dodo-12-37/TrackSense_AppEmbarque/Photos du projet/Application embarquée.png

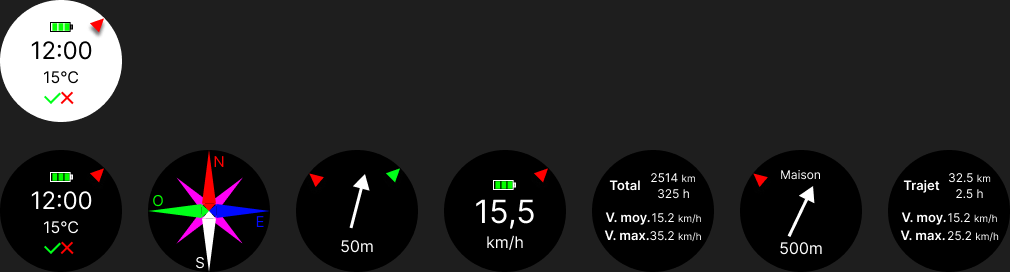
Photos du projet/Application embarquée.png
