dodo-12-37/TrackSense_AppEmbarque/Références Composants/GC9A01 - TFT LCD Display Module/Composant Acheté - Écran GC9A01.png

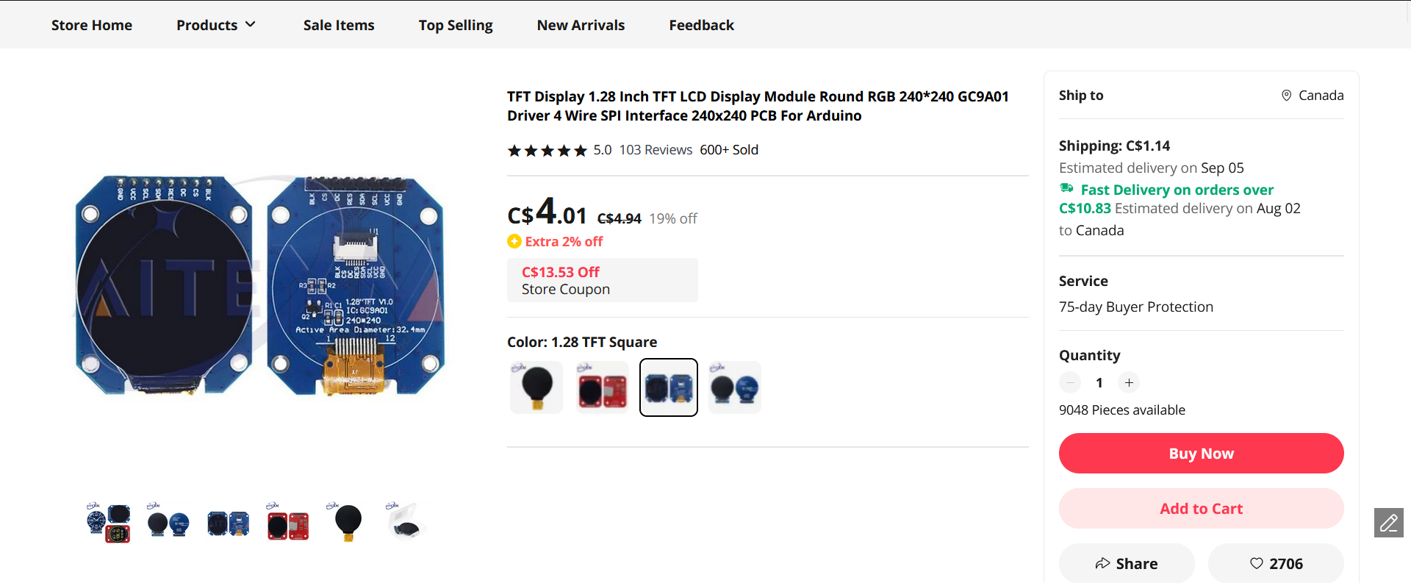
Références Composants/GC9A01 - TFT LCD Display Module/Composant Acheté - Écran GC9A01.png
