dodo-12-37/TrackSense_AppEmbarque/Références Composants/GC9A01 - TFT LCD Display Module/Connection Similar GC9A01 Modules.png

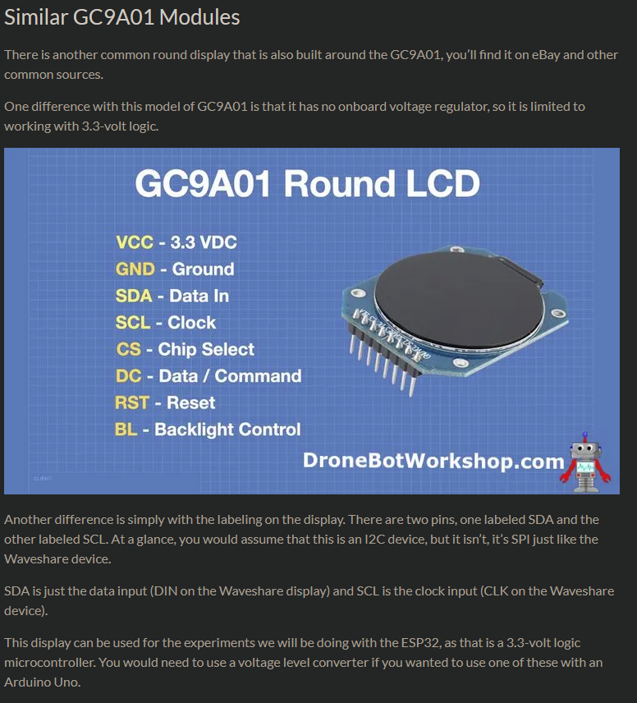
Références Composants/GC9A01 - TFT LCD Display Module/Connection Similar GC9A01 Modules.png
