dodo-12-37/TrackSense_AppEmbarque/Références Composants/GC9A01 - TFT LCD Display Module/Diagramme PINs.png

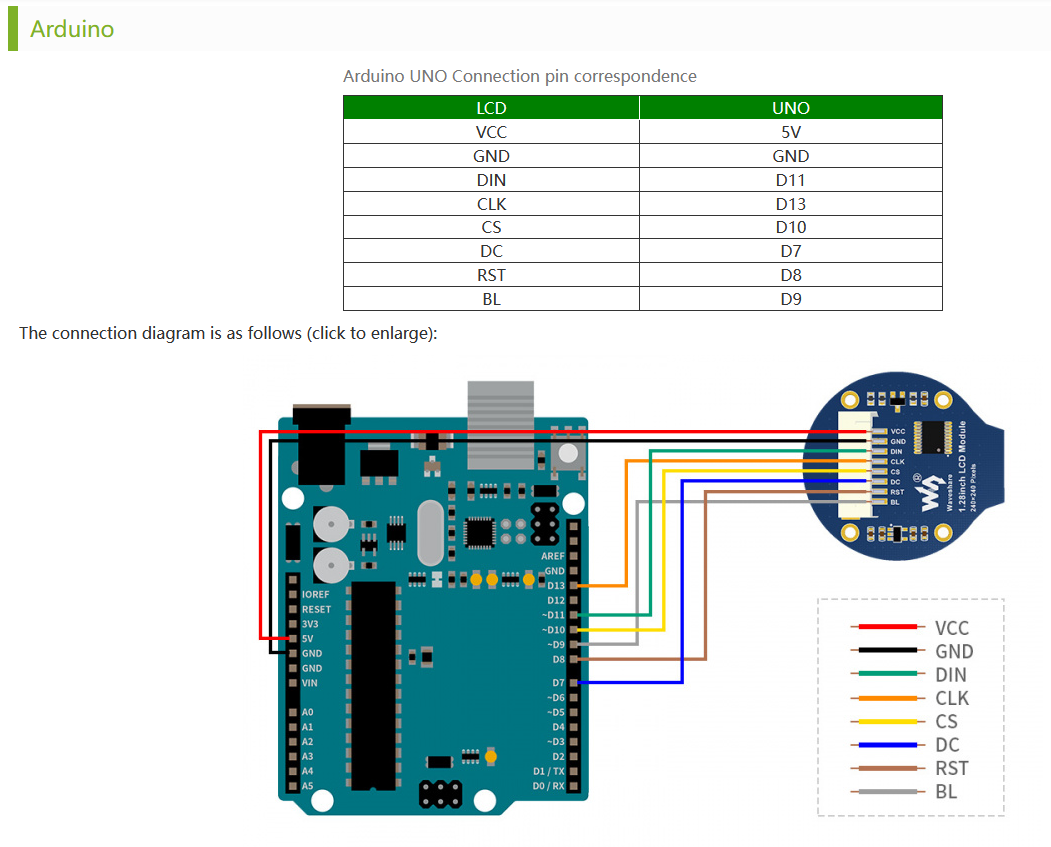
Références Composants/GC9A01 - TFT LCD Display Module/Diagramme PINs.png
