dodo-12-37/TrackSense_AppEmbarque/Références Composants/GC9A01 - TFT LCD Display Module/Dimension Sensor ER-TFTM1.28-1 with No Touch Panel Outline Drawing.png

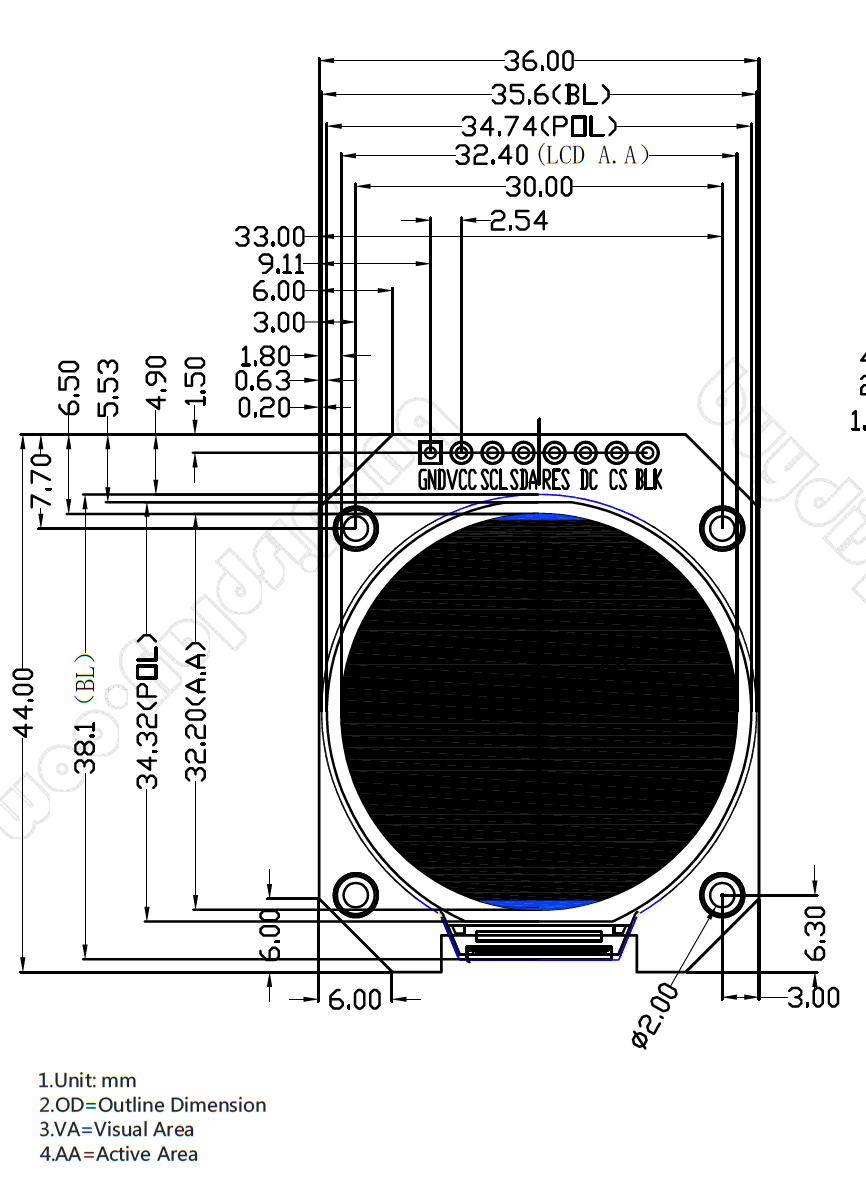
Références Composants/GC9A01 - TFT LCD Display Module/Dimension Sensor ER-TFTM1.28-1 with No Touch Panel Outline Drawing.png
