dodo-12-37/TrackSense_AppEmbarque/Références Composants/GC9A01 - TFT LCD Display Module/IPS-LCD-1.28-240x240-Round-Display-GC9A01-Square-PCB.jpg

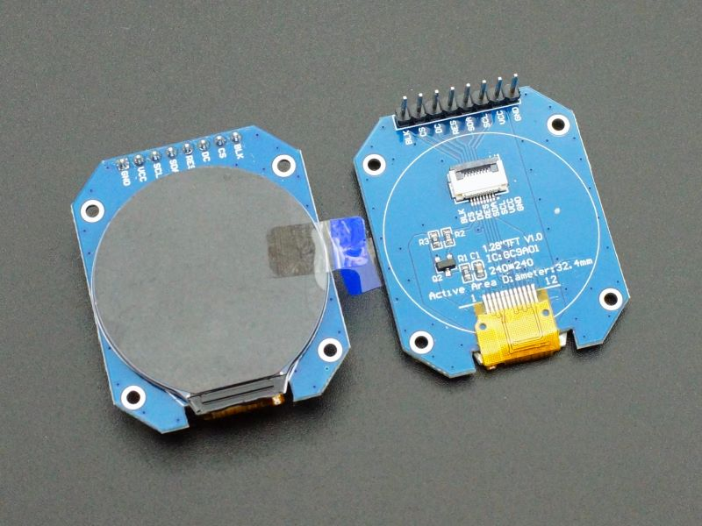
Références Composants/GC9A01 - TFT LCD Display Module/IPS-LCD-1.28-240x240-Round-Display-GC9A01-Square-PCB.jpg
