dodo-12-37/TrackSense_AppEmbarque/Références Composants/GC9A01 - TFT LCD Display Module/TFT LCD Display Module GC9A01 - Mesure Physique.jpg

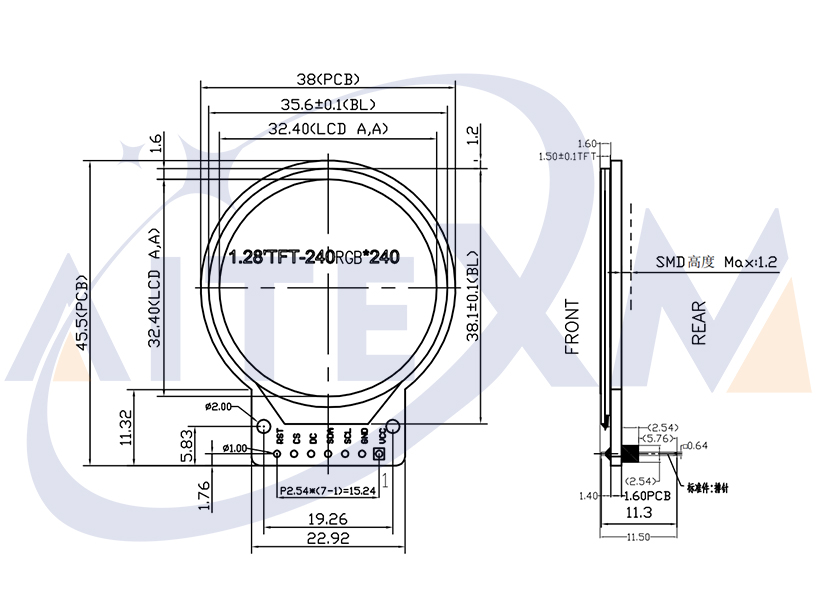
Références Composants/GC9A01 - TFT LCD Display Module/TFT LCD Display Module GC9A01 - Mesure Physique.jpg
