dodo-12-37/TrackSense_AppEmbarque/Références Composants/GY-87 - Accéléromètre, Gyroscope, Boussole & Température/Composant Acheté - GY-87.png

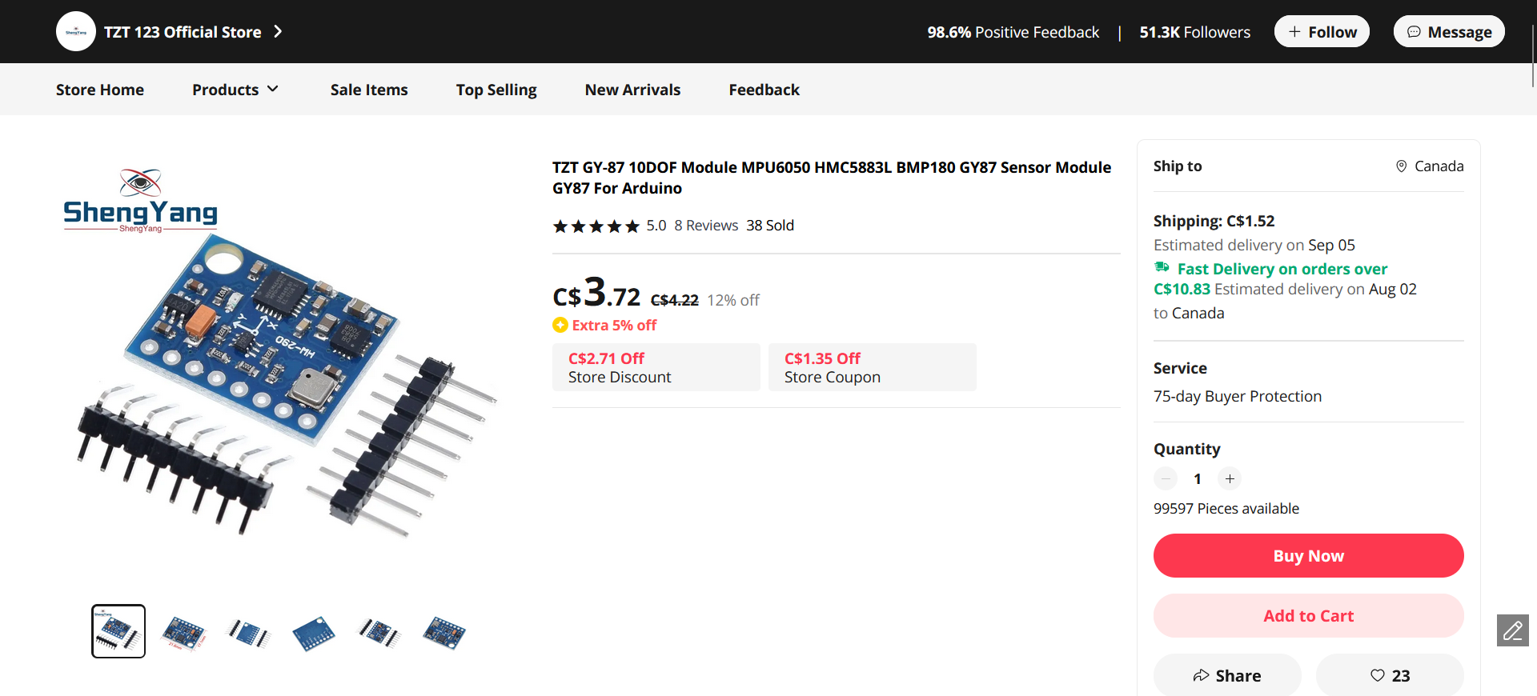
Références Composants/GY-87 - Accéléromètre, Gyroscope, Boussole & Température/Composant Acheté - GY-87.png
