dodo-12-37/TrackSense_AppEmbarque/Références Composants/GY-87 - Accéléromètre, Gyroscope, Boussole & Température/Dessous Sensor.jpg

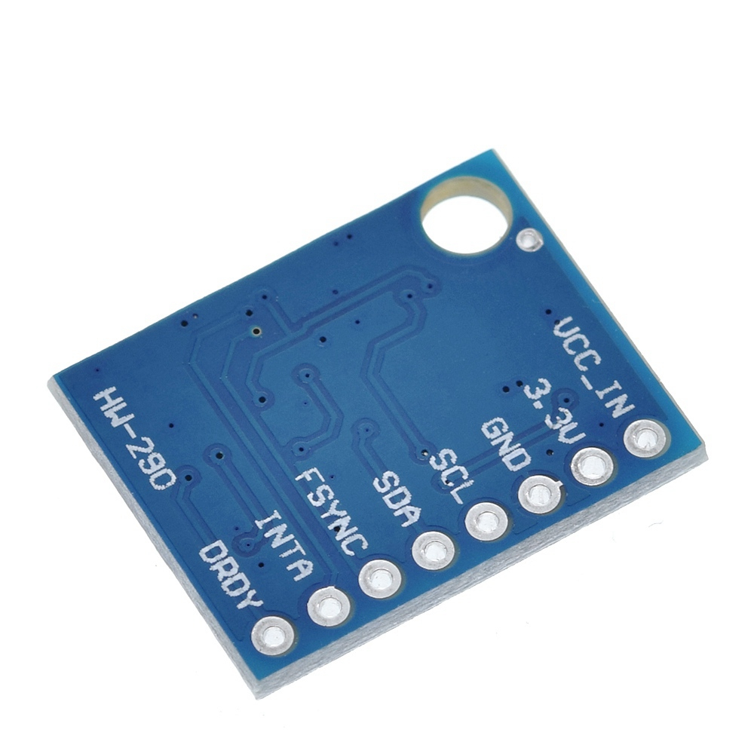
Références Composants/GY-87 - Accéléromètre, Gyroscope, Boussole & Température/Dessous Sensor.jpg
