dodo-12-37/TrackSense_AppEmbarque/Références Composants/GY-87 - Accéléromètre, Gyroscope, Boussole & Température/GY-87-Module-wire-4.jpg

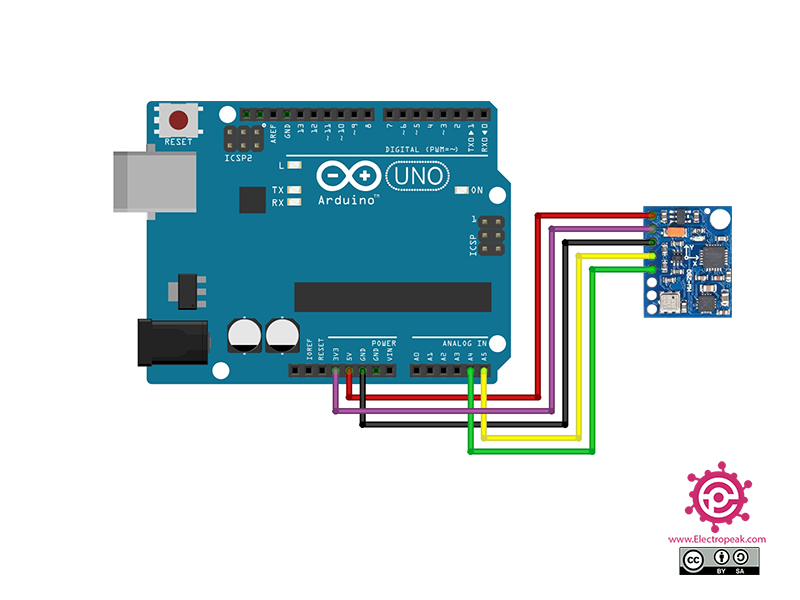
Références Composants/GY-87 - Accéléromètre, Gyroscope, Boussole & Température/GY-87-Module-wire-4.jpg
