dodo-12-37/TrackSense_AppEmbarque/Références Composants/GY-87 - Accéléromètre, Gyroscope, Boussole & Température/GY-87-Pin-2.jpg

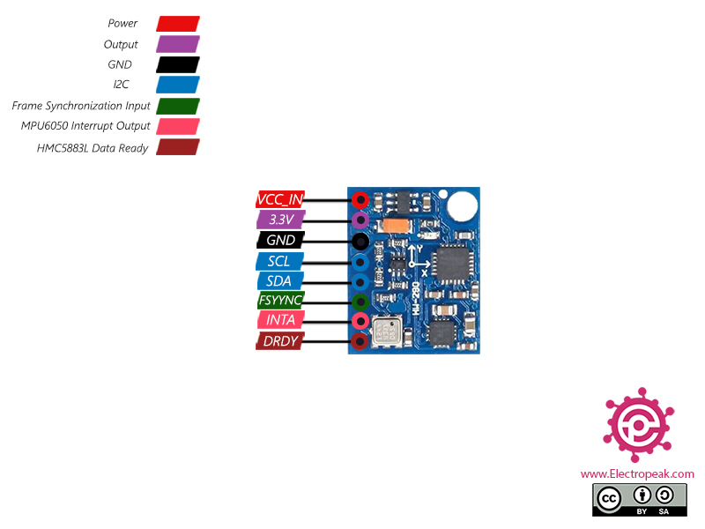
Références Composants/GY-87 - Accéléromètre, Gyroscope, Boussole & Température/GY-87-Pin-2.jpg
