dodo-12-37/TrackSense_AppEmbarque/Références Composants/LILYGO T-SIM7000G - ESP32/Composant Acheté - LILYGO T-SIM7000G 16MB.png

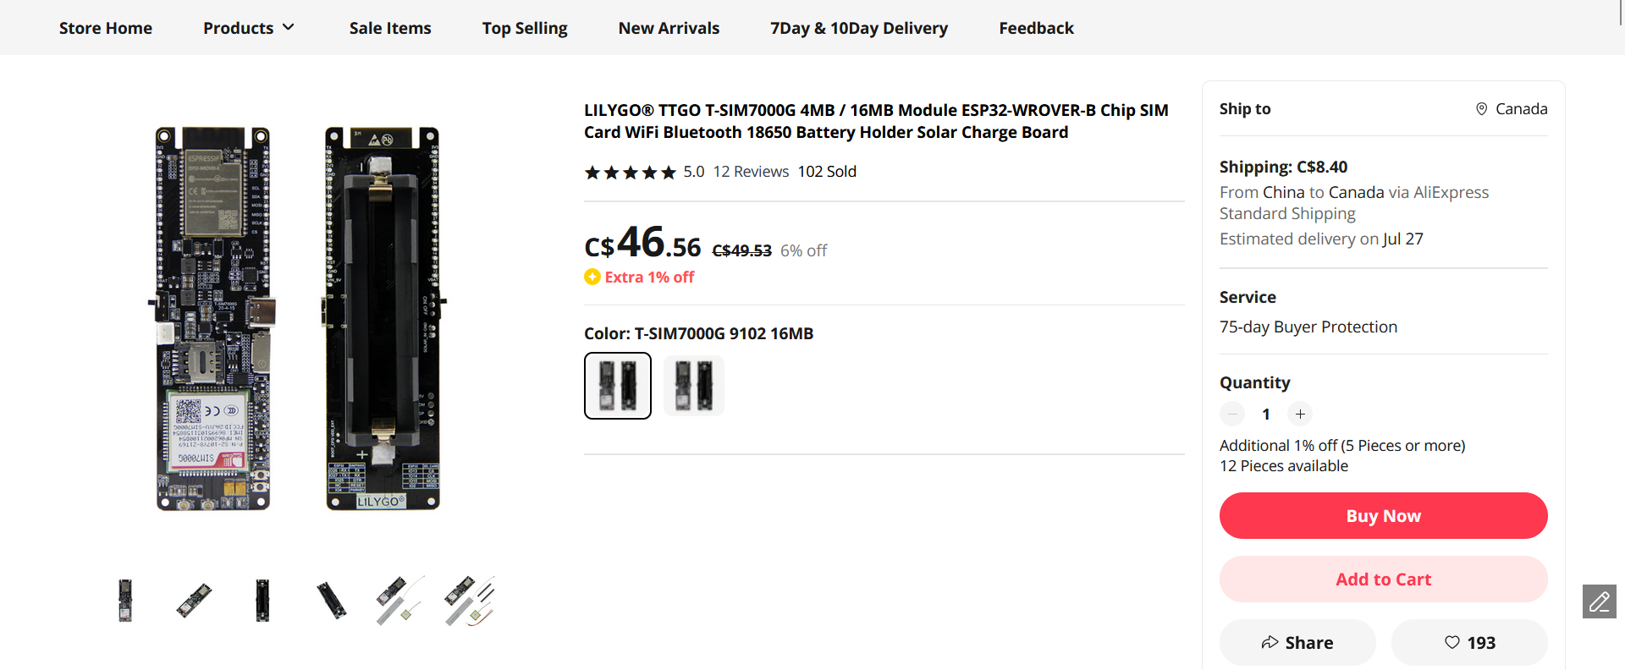
Références Composants/LILYGO T-SIM7000G - ESP32/Composant Acheté - LILYGO T-SIM7000G 16MB.png
