dodo-12-37/TrackSense_AppEmbarque/Références Composants/LILYGO T-SIM7000G - ESP32/Description Aliexpress.png

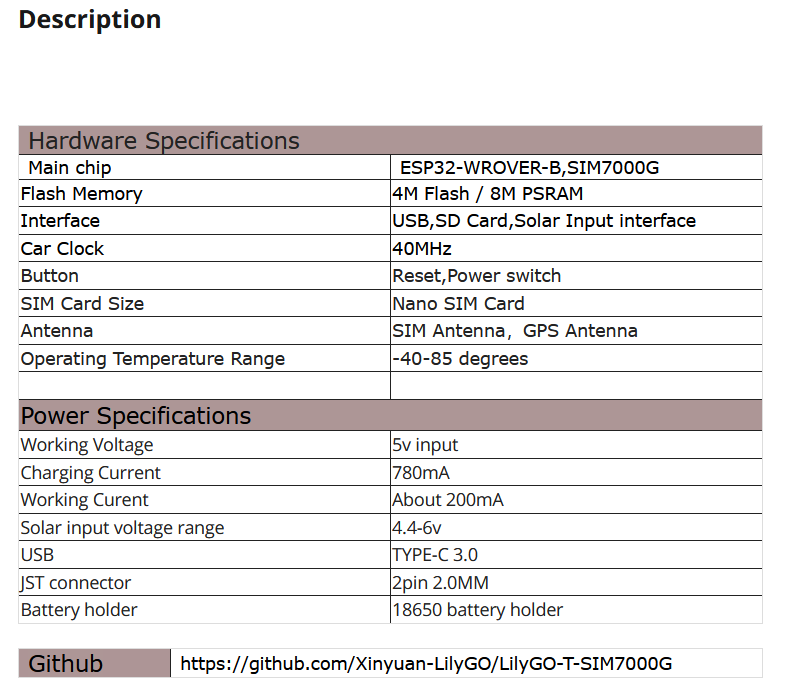
Références Composants/LILYGO T-SIM7000G - ESP32/Description Aliexpress.png
