dodo-12-37/TrackSense_AppEmbarque/Références Composants/LILYGO T-SIM7000G - ESP32/Dimension de la Plaquette V1.1.png

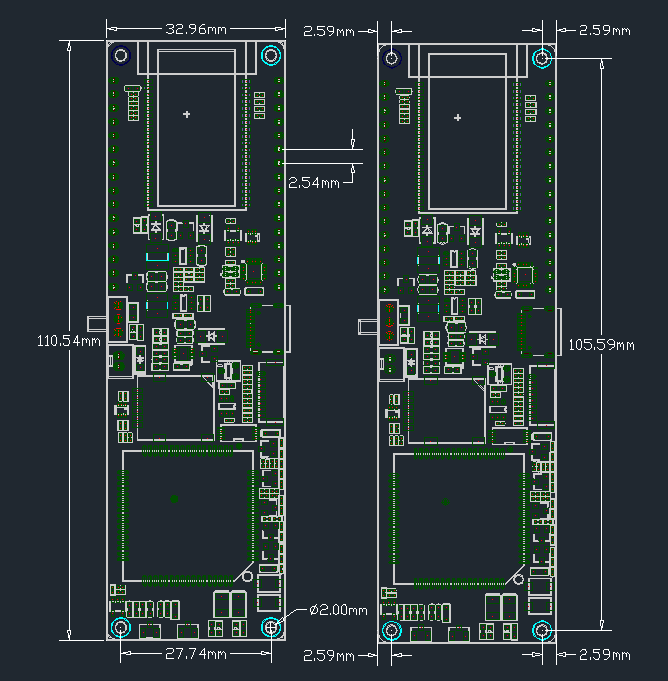
Références Composants/LILYGO T-SIM7000G - ESP32/Dimension de la Plaquette V1.1.png
