dodo-12-37/TrackSense_AppEmbarque/Références Composants/LILYGO T-SIM7000G - ESP32/Emplacement des composantes 1 - V1.1.jpg

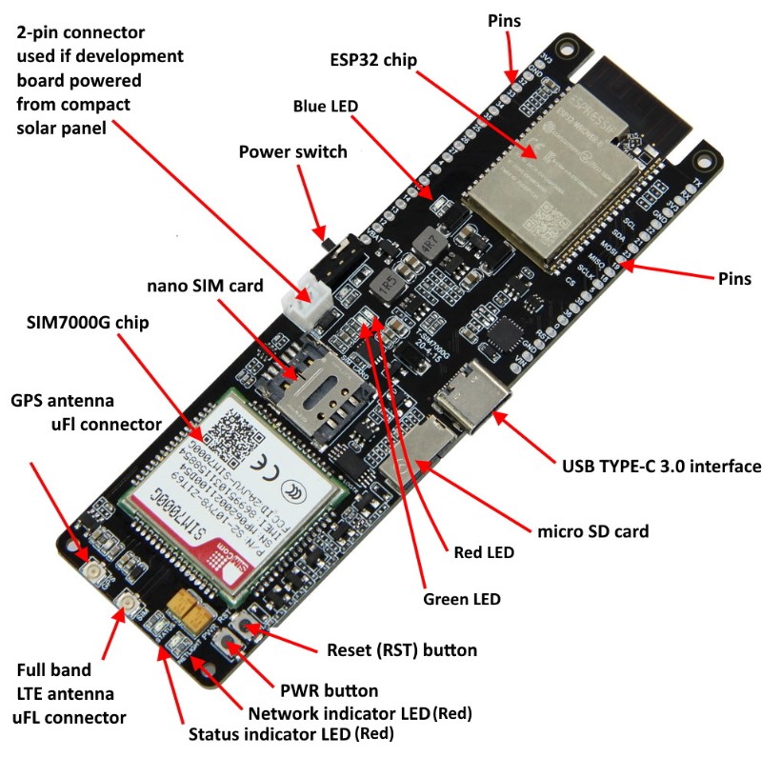
Références Composants/LILYGO T-SIM7000G - ESP32/Emplacement des composantes 1 - V1.1.jpg
