dodo-12-37/TrackSense_AppEmbarque/Références Composants/LILYGO T-SIM7000G - ESP32/GPS/AT command in the serial terminal.png

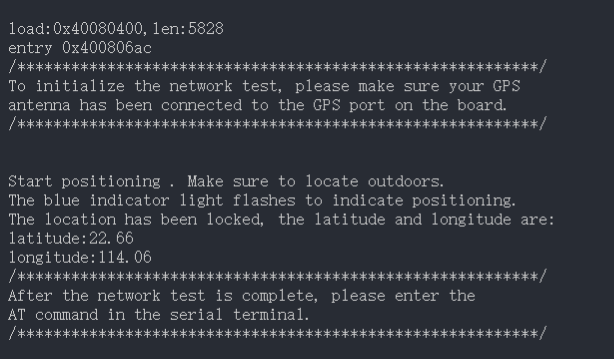
Références Composants/LILYGO T-SIM7000G - ESP32/GPS/AT command in the serial terminal.png
