dodo-12-37/TrackSense_AppEmbarque/Références Composants/LILYGO T-SIM7000G - ESP32/Lilygo GitHub - Modèle 3D/Boitier Générique Lilygo - All - Vue Isométrique NE.jpg

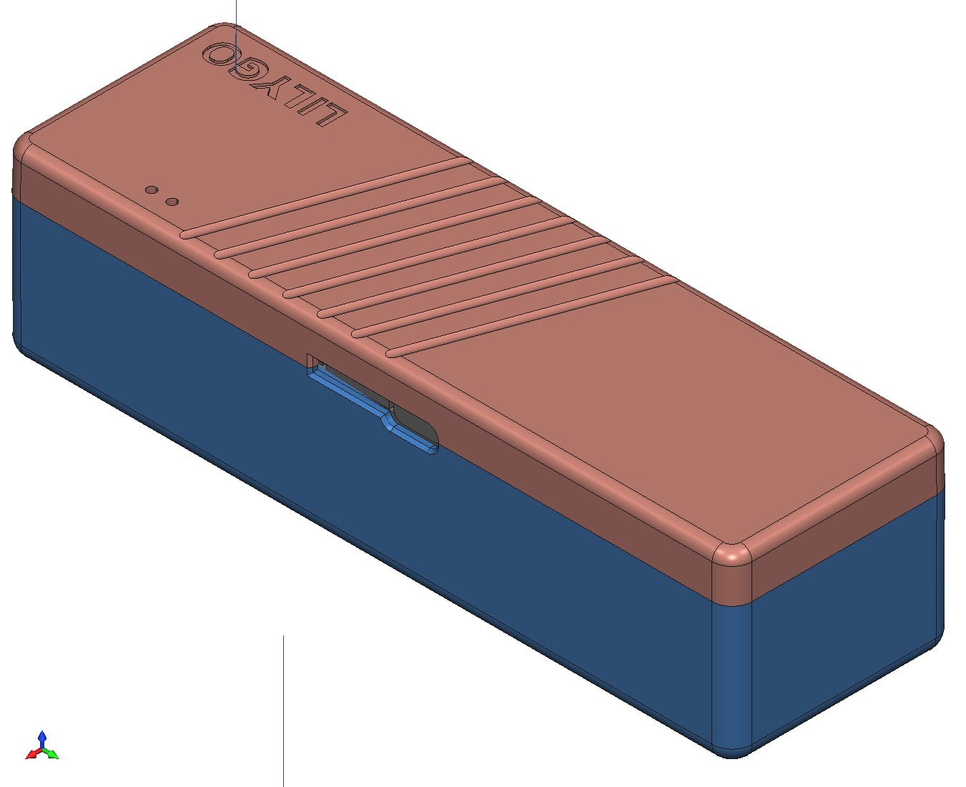
Références Composants/LILYGO T-SIM7000G - ESP32/Lilygo GitHub - Modèle 3D/Boitier Générique Lilygo - All - Vue Isométrique NE.jpg
