dodo-12-37/TrackSense_AppEmbarque/Références Composants/LILYGO T-SIM7000G - ESP32/LILYGO-SIM7000G-ESP32-Différence entre les versions.jpg

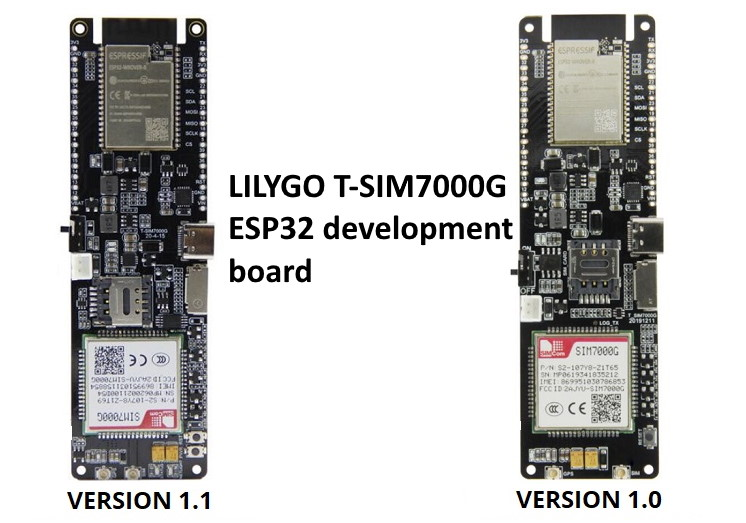
Références Composants/LILYGO T-SIM7000G - ESP32/LILYGO-SIM7000G-ESP32-Différence entre les versions.jpg
