dodo-12-37/TrackSense_AppEmbarque/Références Composants/LILYGO T-SIM7000G - ESP32/Modification de la Nouvelle Version 1.1.png

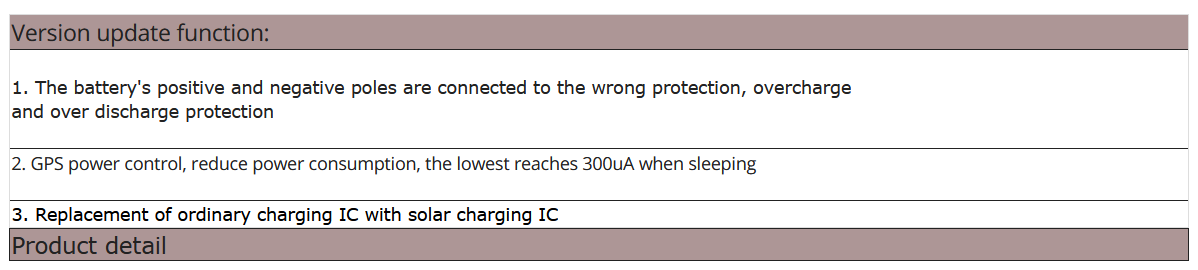
Références Composants/LILYGO T-SIM7000G - ESP32/Modification de la Nouvelle Version 1.1.png
