dodo-12-37/TrackSense_AppEmbarque/Références Composants/PCB TrackSense/Choix couleurs PCB.jpg

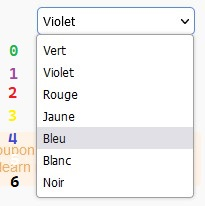
Références Composants/PCB TrackSense/Choix couleurs PCB.jpg
