dodo-12-37/TrackSense_AppEmbarque/Références Composants/PCB TrackSense/Inspiration externe/Capture d’écran 2023-07-04 142751.png

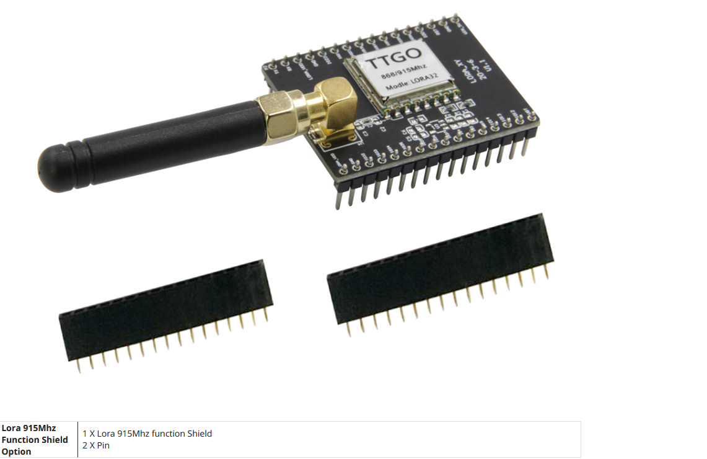
Références Composants/PCB TrackSense/Inspiration externe/Capture d’écran 2023-07-04 142751.png
