dodo-12-37/TrackSense_AppEmbarque/Références Composants/PCB TrackSense/V1.0/Dessus 3D TrackSense V1.0.jpg

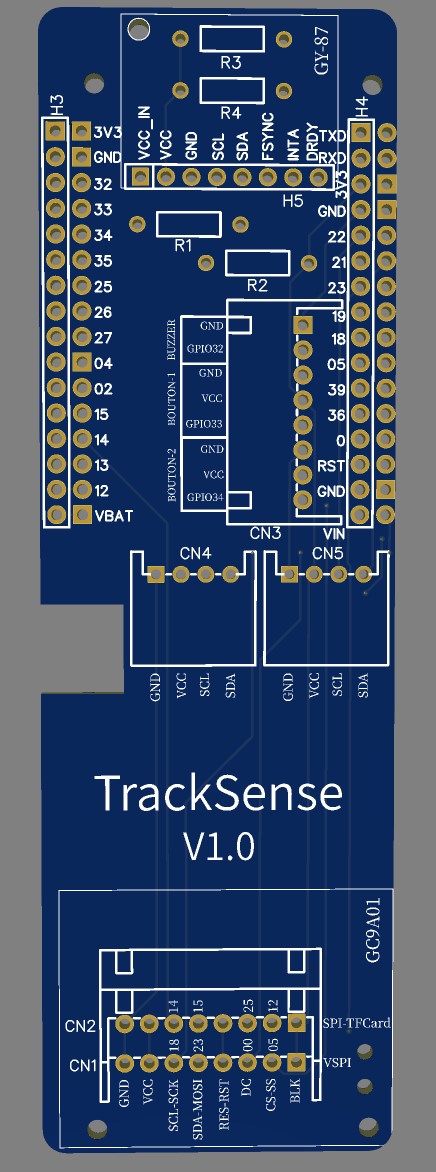
Références Composants/PCB TrackSense/V1.0/Dessus 3D TrackSense V1.0.jpg
