dodo-12-37/TrackSense_AppEmbarque/Références Composants/SFM-27 ou SFM-20B - Speaker Alarme/Composants Acheté - Buzzer Piézo.png

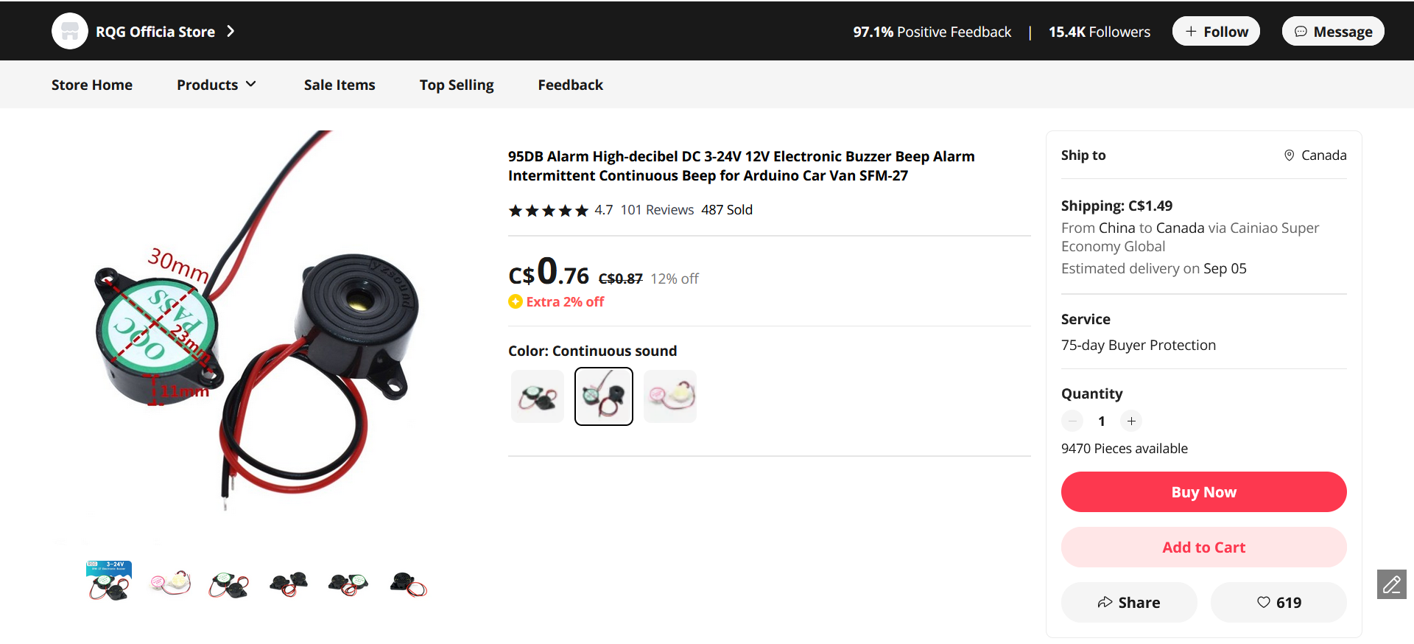
Références Composants/SFM-27 ou SFM-20B - Speaker Alarme/Composants Acheté - Buzzer Piézo.png
