dodo-12-37/TrackSense_AppEmbarque/Références Composants/SFM-27 ou SFM-20B - Speaker Alarme/Dessus & Dessous Sensor 2.jpg

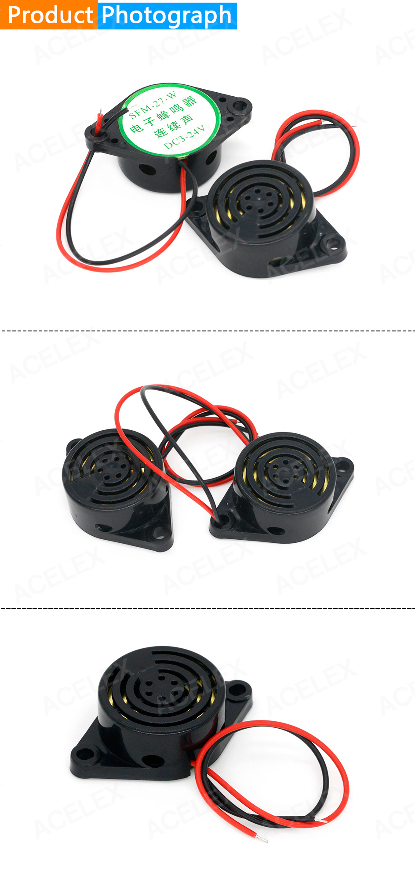
Références Composants/SFM-27 ou SFM-20B - Speaker Alarme/Dessus & Dessous Sensor 2.jpg
