dodo-12-37/TrackSense_AppEmbarque/Références Composants/SFM-27 ou SFM-20B - Speaker Alarme/Dimension_SFM-20B.jpg

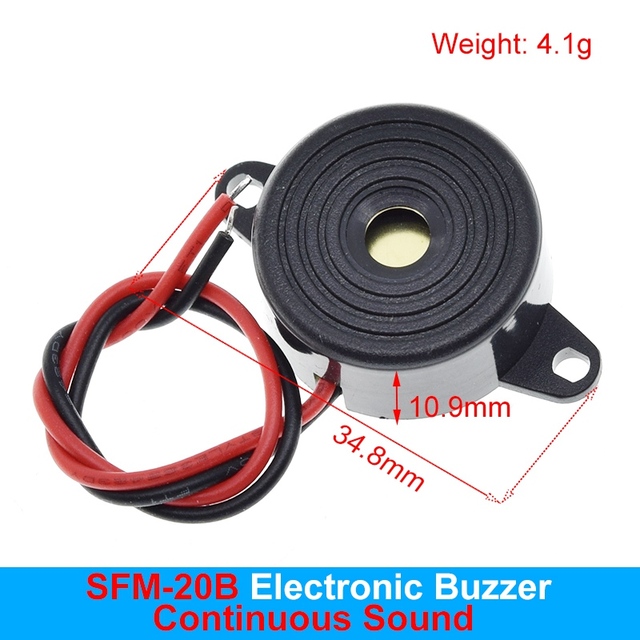
Références Composants/SFM-27 ou SFM-20B - Speaker Alarme/Dimension_SFM-20B.jpg
