dodo-12-37/TrackSense_AppEmbarque/Références Composants/SFM-27 ou SFM-20B - Speaker Alarme/SFM-27/Paramètres du Produit SFM-27.jpg

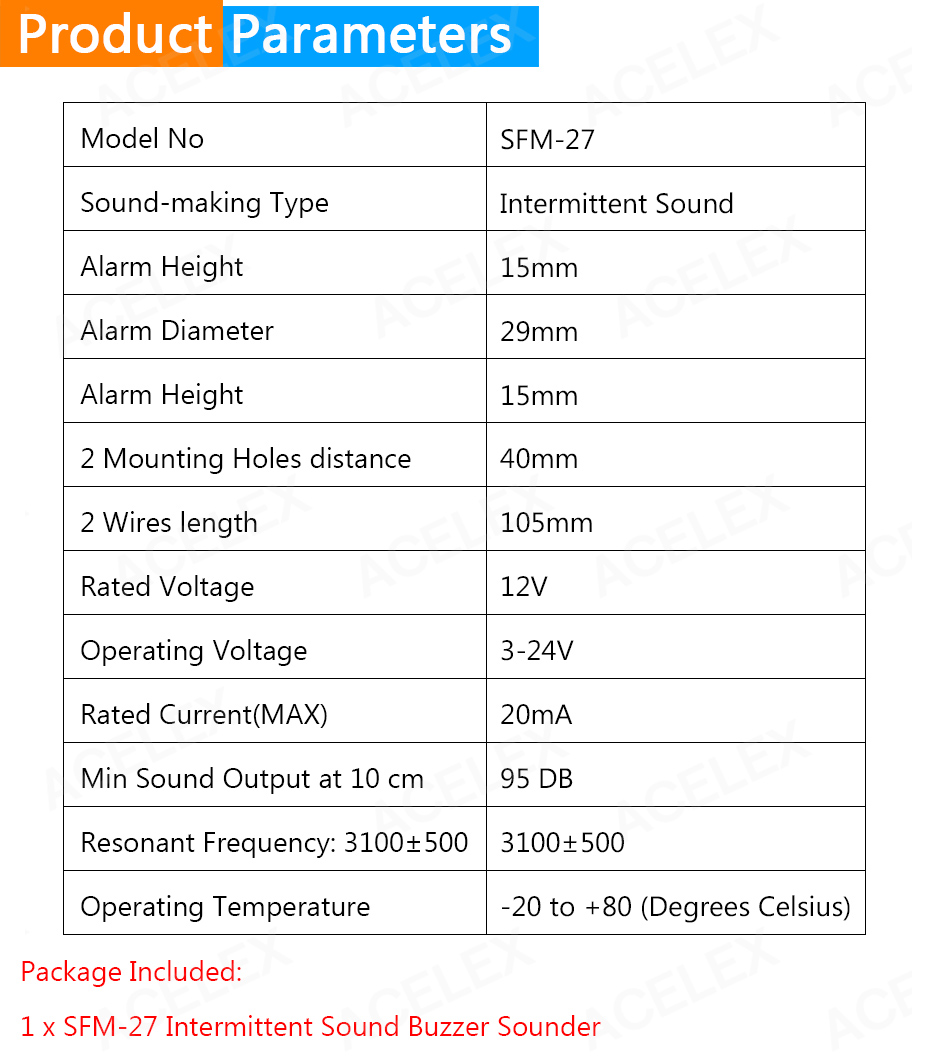
Références Composants/SFM-27 ou SFM-20B - Speaker Alarme/SFM-27/Paramètres du Produit SFM-27.jpg
