dodo-12-37/TrackSense_AppEmbarque/Références Composants/SFM-27 ou SFM-20B - Speaker Alarme/Speaker Alarme SFM-20B XHX-2312 (Pt pas celui acheté).jpg

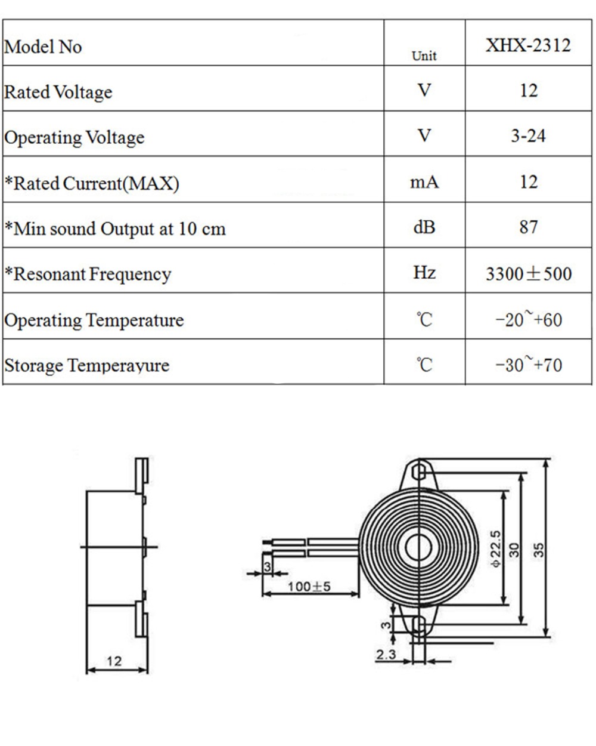
Références Composants/SFM-27 ou SFM-20B - Speaker Alarme/Speaker Alarme SFM-20B XHX-2312 (Pt pas celui acheté).jpg
