dodo-12-37/TrackSense_AppEmbarque/Références Composants/TTP223B - Boutton Tactile/Dessous Sensor.jpg

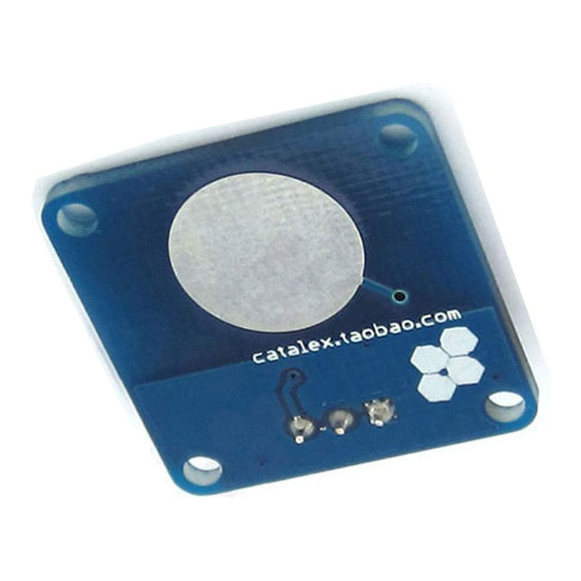
Références Composants/TTP223B - Boutton Tactile/Dessous Sensor.jpg
