dodo-12-37/TrackSense_AppEmbarque/Références Composants/TTP223B - Boutton Tactile/Dessus Sensor.jpg

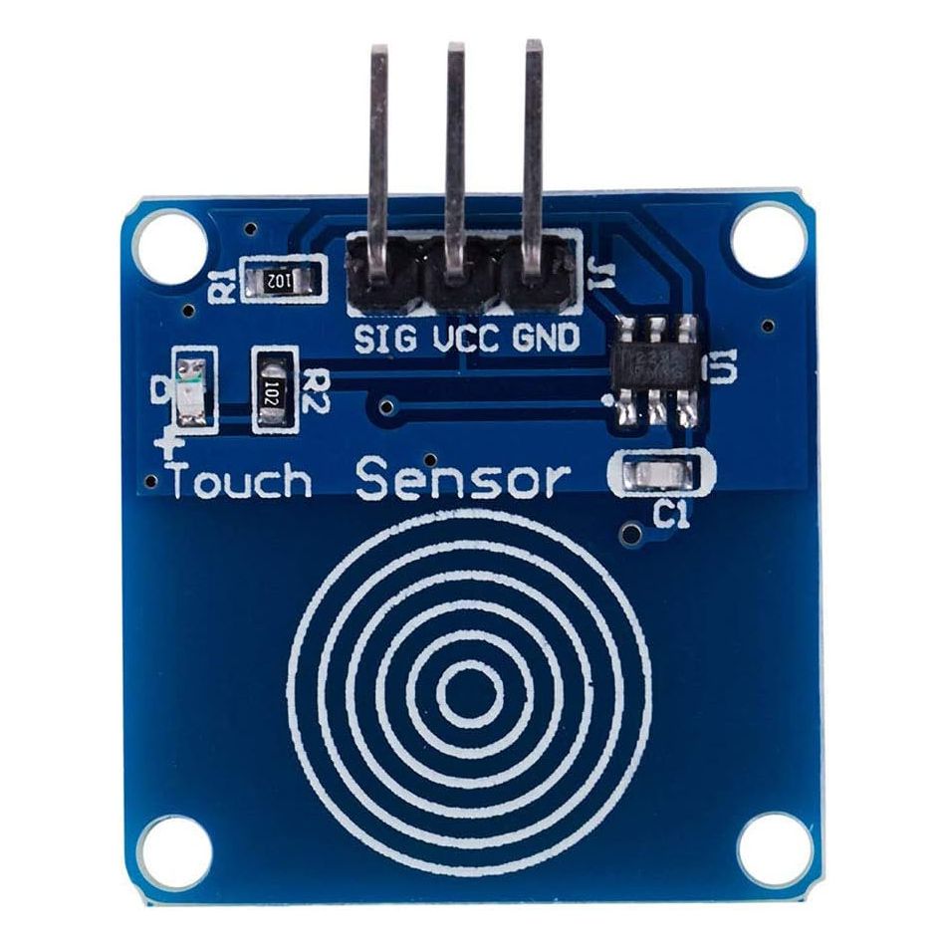
Références Composants/TTP223B - Boutton Tactile/Dessus Sensor.jpg
