dodo-12-37/TrackSense_AppEmbarque/Références Composants/TTP223B - Boutton Tactile/Digital-Sensor-TTP223B-Module-Capacitive2.webp

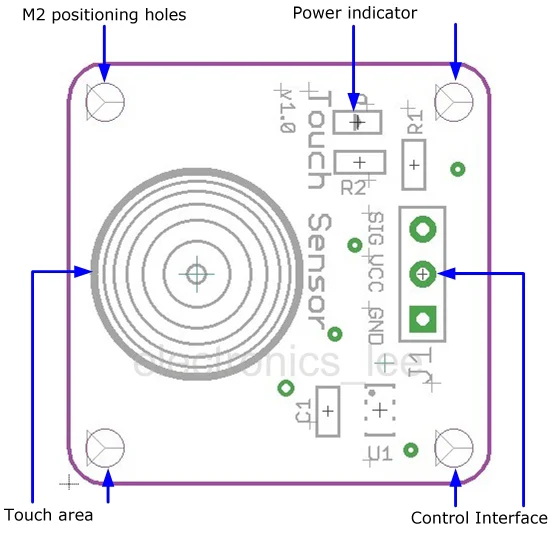
Références Composants/TTP223B - Boutton Tactile/Digital-Sensor-TTP223B-Module-Capacitive2.webp
