dodo-12-37/TrackSense_AppEmbarque/Références Composants/TTP223B - Boutton Tactile/Dimensions 2.JPG

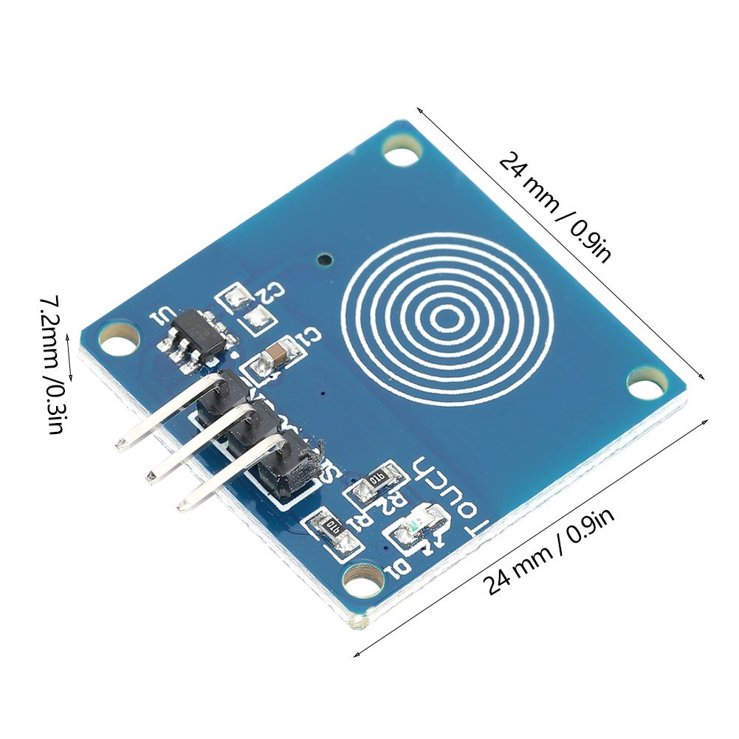
Références Composants/TTP223B - Boutton Tactile/Dimensions 2.JPG
