dodo-12-37/TrackSense_AppEmbarque/Références Composants/TTP223B - Boutton Tactile/Dimensions.JPG

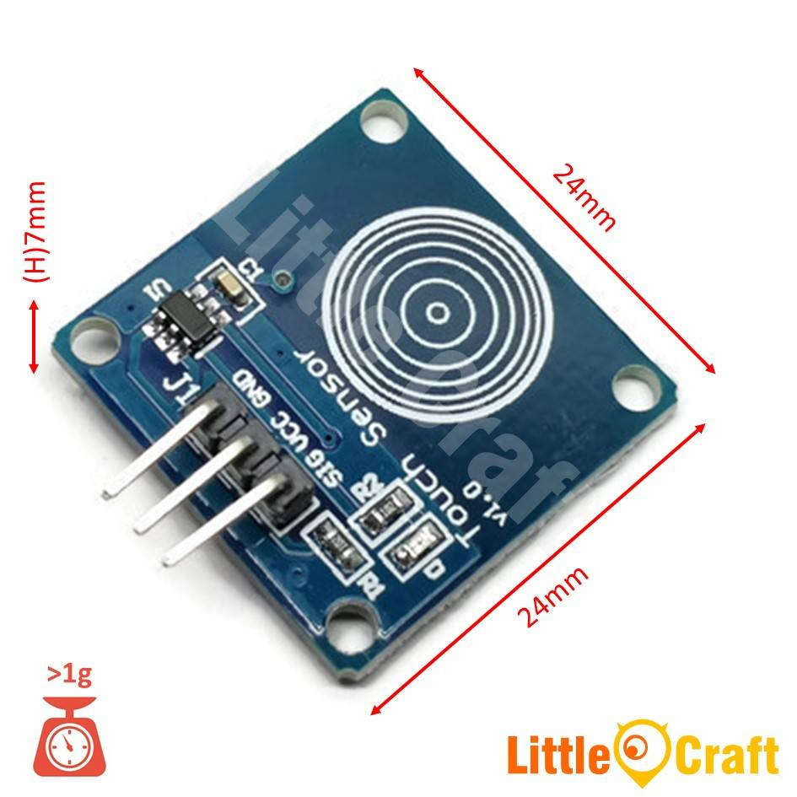
Références Composants/TTP223B - Boutton Tactile/Dimensions.JPG
