dodo-12-37/TrackSense_AppEmbarque/Références Composants/TTP223B - Boutton Tactile/Exemple Connexion Arduino 2.jpg

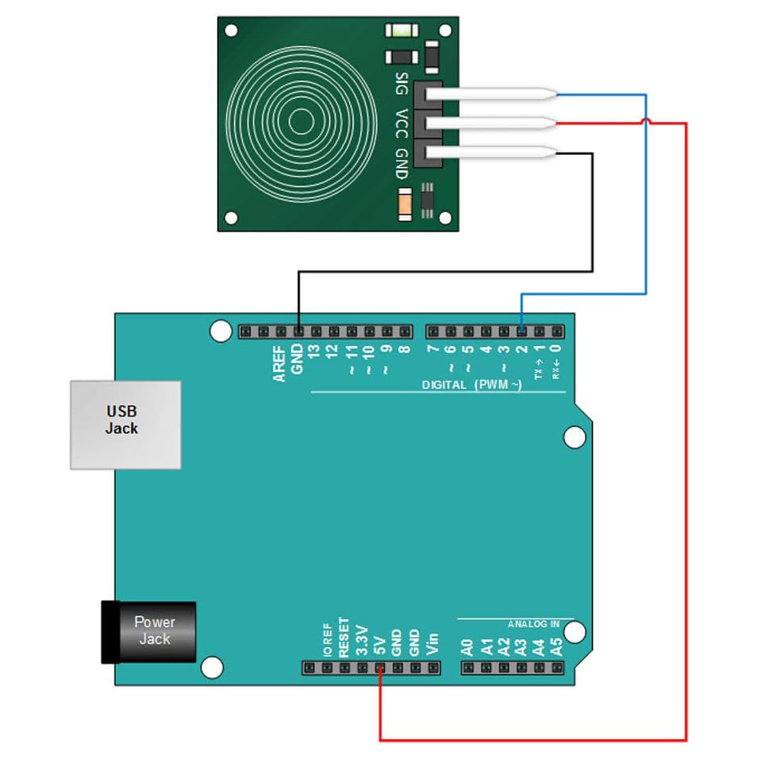
Références Composants/TTP223B - Boutton Tactile/Exemple Connexion Arduino 2.jpg
