dodo-12-37/TrackSense_AppEmbarque/Références Composants/TTP223B - Boutton Tactile/Exemple Connexion.jpg

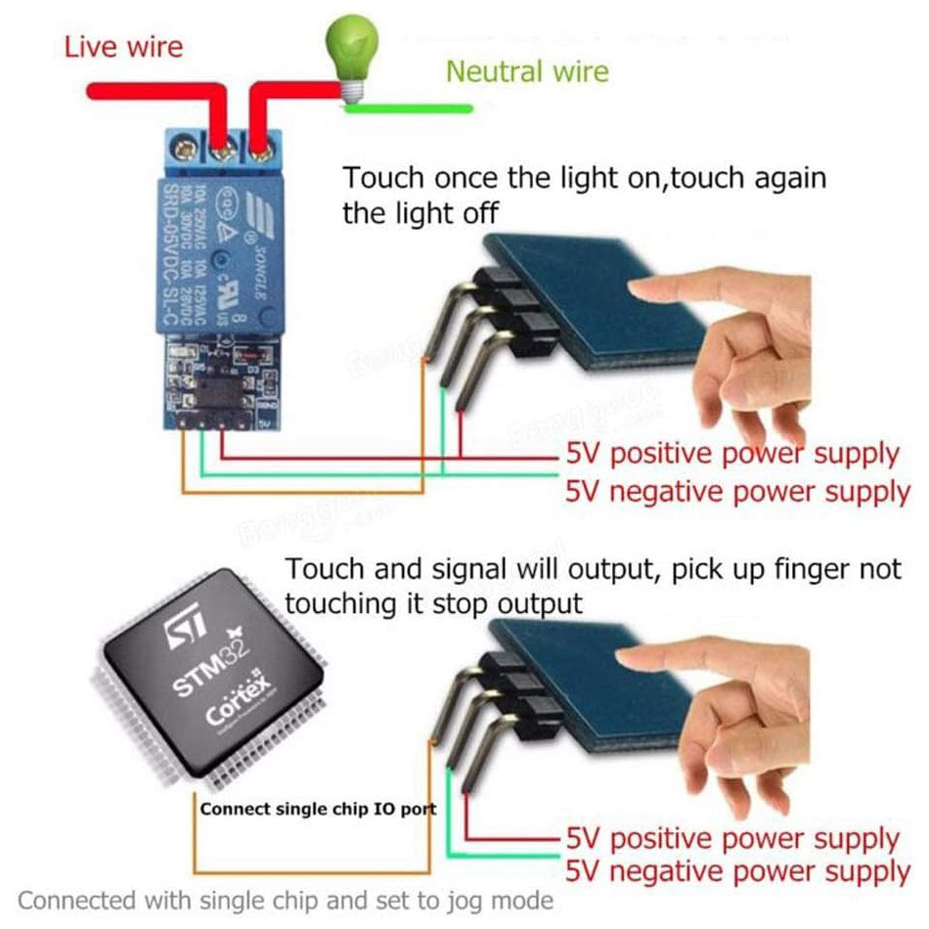
Références Composants/TTP223B - Boutton Tactile/Exemple Connexion.jpg
