dodo-12-37/TrackSense_AppEmbarque/src/AppEmbarqueeTS/src/Modules/AccelerometerMPU6050.cpp

#include "Modules/AccelerometerMPU6050.h"



AccelerometerMPU6050::AccelerometerMPU6050(TrackSenseProperties* trackSenseProperties) : _trackSenseProperties(trackSenseProperties)
{
}

AccelerometerMPU6050::~AccelerometerMPU6050()
{
}

void AccelerometerMPU6050::tick()
{
    ;
}
