dodo-12-37/TrackSense_AppEmbarque/src/AppEmbarqueeTS/src/Modules/Buzzer.cpp

#include "Modules/Buzzer.h"



Buzzer::Buzzer(TrackSenseProperties* trackSenseProperties) : _trackSenseProperties(trackSenseProperties)
{
    pinMode(PIN_BUZZER, OUTPUT);
}

Buzzer::~Buzzer()
{
}

void Buzzer::tick()
{
    if (this->_trackSenseProperties->PropertiesBuzzer._isBuzzerOn)
    {
        tone(PIN_BUZZER, 500, 100);
        this->_trackSenseProperties->PropertiesBuzzer._isBuzzerOn = false;
    }
}
