dodo-12-37/TrackSense_AppEmbarque/src/AppEmbarqueeTS/src/Modules/CompassHMC5883L.cpp

#include "Modules/CompassHMC5883L.h"



CompassHMC5883L::CompassHMC5883L(TrackSenseProperties* trackSenseProperties) : _trackSenseProperties(trackSenseProperties)
{
}

CompassHMC5883L::~CompassHMC5883L()
{
}

void CompassHMC5883L::tick()
{
    ;
}
