dodo-12-37/TrackSense_AppEmbarque/src/AppEmbarqueeTS/src/Modules/GyroscopeMPU6050.cpp

#include "Modules/GyroscopeMPU6050.h"



GyroscopeMPU6050::GyroscopeMPU6050(TrackSenseProperties* trackSenseProperties) : _trackSenseProperties(trackSenseProperties)
{
}

GyroscopeMPU6050::~GyroscopeMPU6050()
{
}

void GyroscopeMPU6050::tick()
{
    ;
}
